ASA-Rocketry/Project-Viikate/code/app/include/sensors.h

#pragma once

#include <stdint.h>
#include <zephyr/kernel.h>

#include "math/linmath.h"

typedef struct {
    uint64_t timestamp_ns;
    vec3 acceleration;
    vec3 angular_rate;
} imu_sample_t;

typedef struct {
    uint64_t timestamp_ns;
    float temperature;
    float pressure;
} barometer_sample_t;

extern struct k_msgq imu_msgq;
extern struct k_msgq barometer_msgq;

void task_barometer_read(void *arg1, void *arg2, void *arg3);

int imu_init(const struct device *imu);
int barometer_init(const struct device *barometer);
